MauricioPimenta/Drone_Build/Teste_IMU_Bebop/PixHawk/2026.03.09_TakeOff_and_Hover/PX4_Flight_Review/RAW_Acceleration_X.png

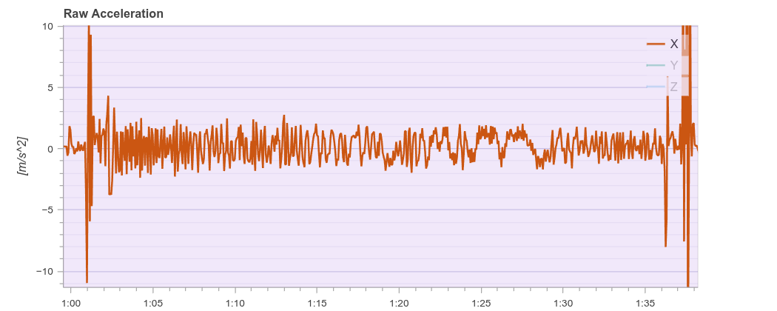
Teste_IMU_Bebop/PixHawk/2026.03.09_TakeOff_and_Hover/PX4_Flight_Review/RAW_Acceleration_X.png
