MauricioPimenta/Drone_Build/Teste_IMU_Bebop/PixHawk/2026.03.09_TakeOff_and_Hover/PX4_Flight_Review/Vibration_Metrics.png

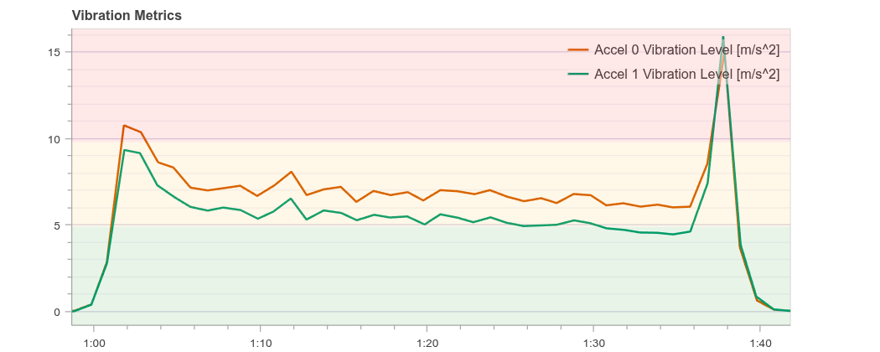
Teste_IMU_Bebop/PixHawk/2026.03.09_TakeOff_and_Hover/PX4_Flight_Review/Vibration_Metrics.png
